pyrex8/leaf-energy-meter/images/arduino.png

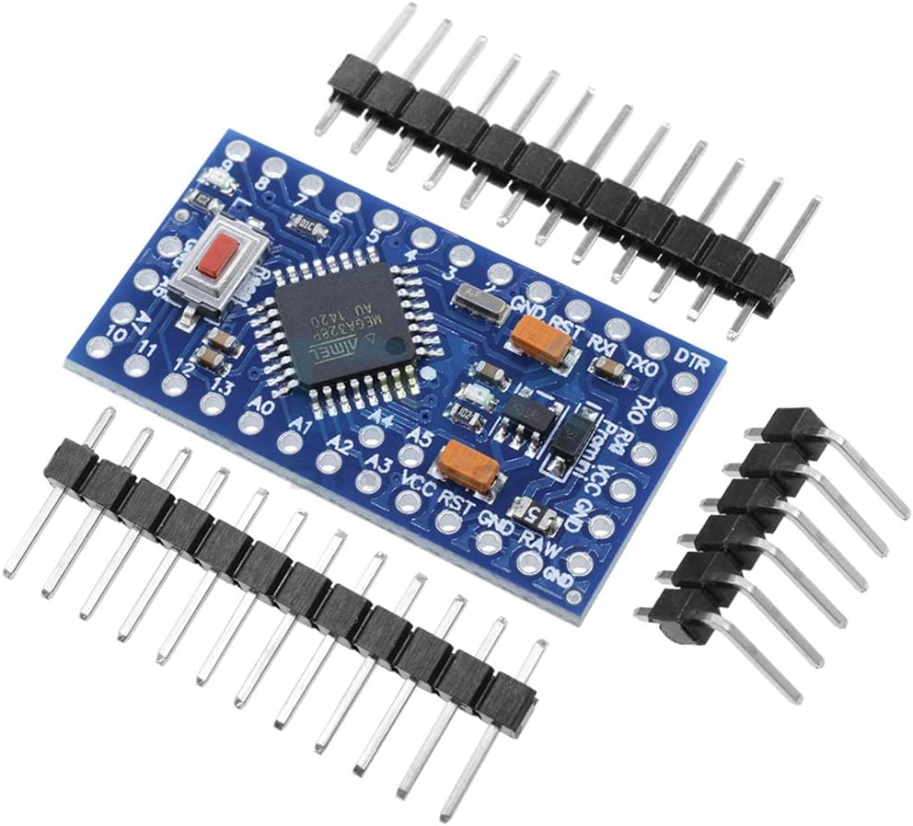
images/arduino.png
