pyrex8/leaf-energy-meter/images/can.png

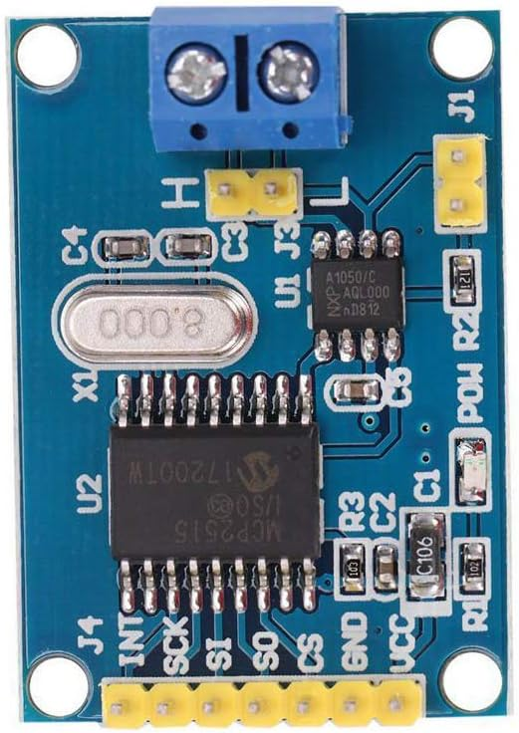
images/can.png
