pyrex8/leaf-energy-meter/images/display_bezel_black_tape.jpg

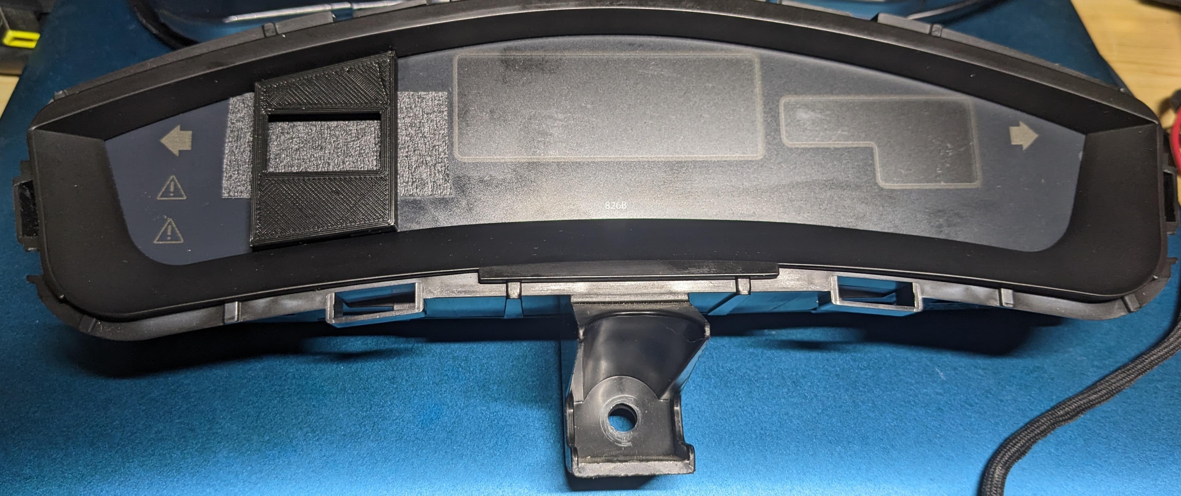
images/display_bezel_black_tape.jpg
