pyrex8/leaf-energy-meter/images/display_connector.jpg

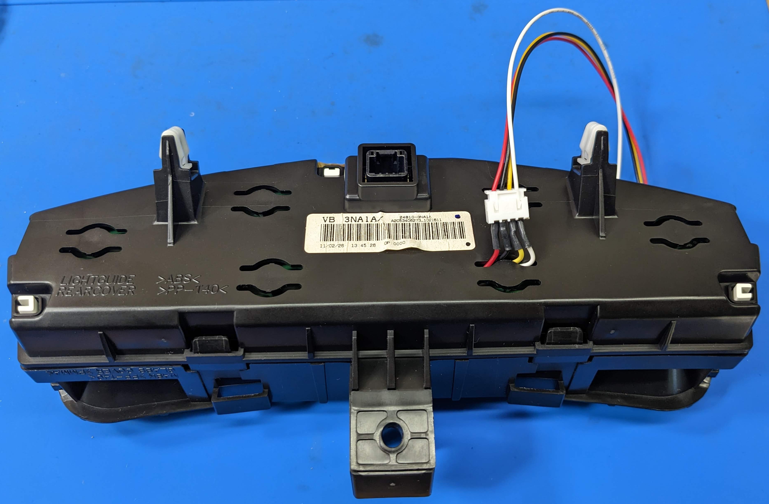
images/display_connector.jpg
