pyrex8/leaf-energy-meter/images/display_mounted.jpg

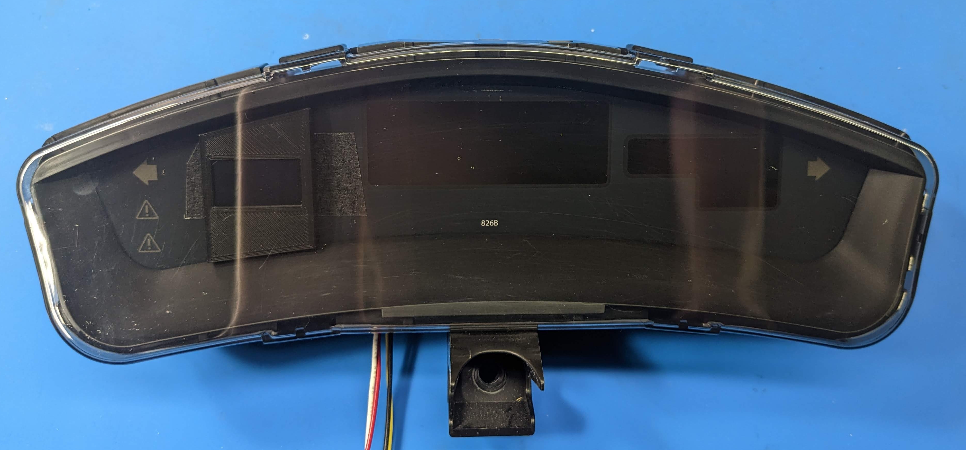
images/display_mounted.jpg
