pyrex8/leaf-energy-meter/images/enclosure.png

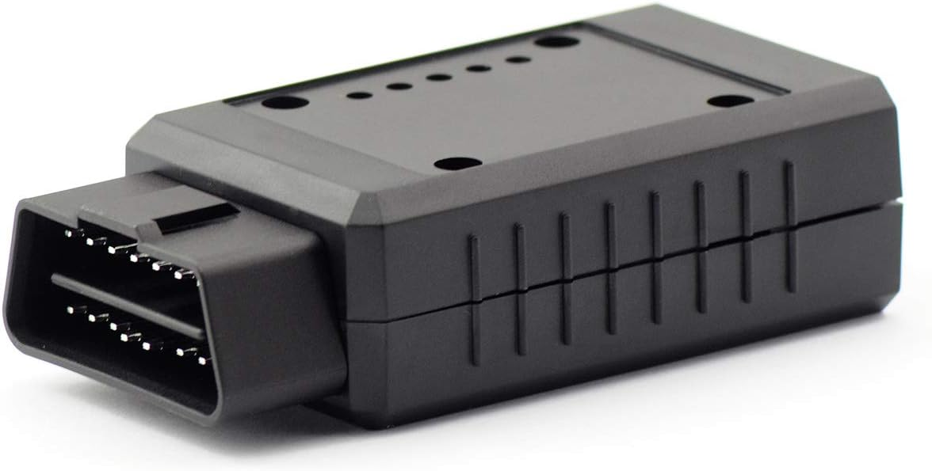
images/enclosure.png
