pyrex8/leaf-energy-meter/images/jst.png

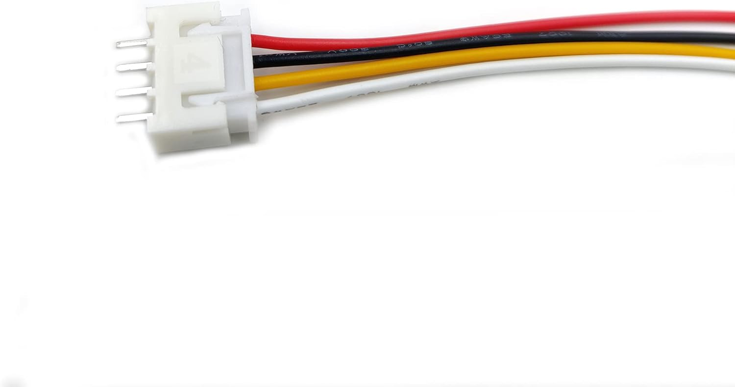
images/jst.png
