pyrex8/leaf-energy-meter/images/meter_pcb_in_case.jpg

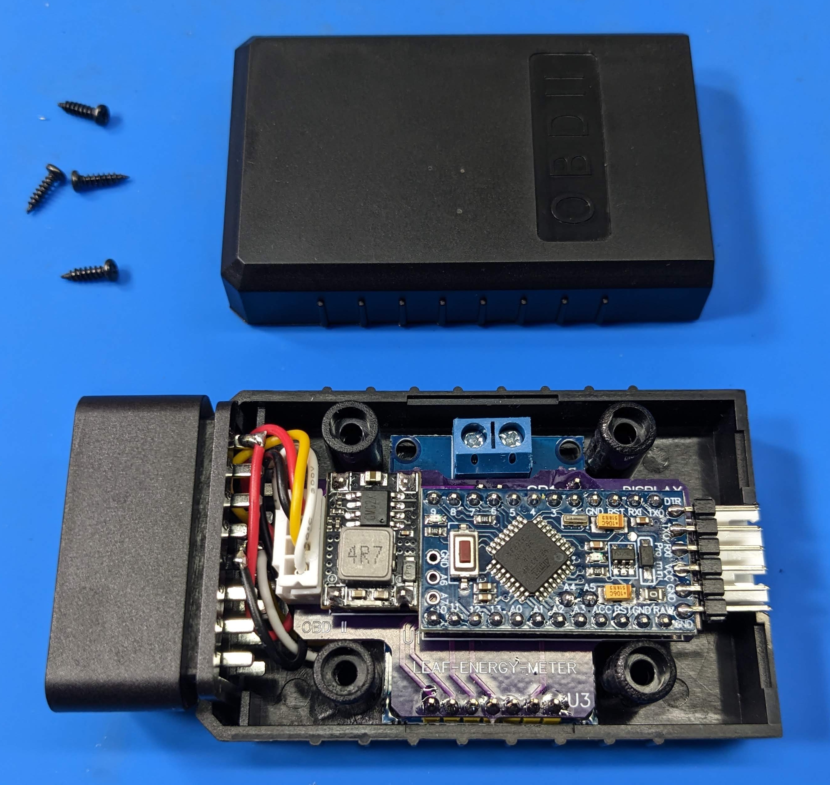
images/meter_pcb_in_case.jpg
