pyrex8/leaf-energy-meter/images/oled.png

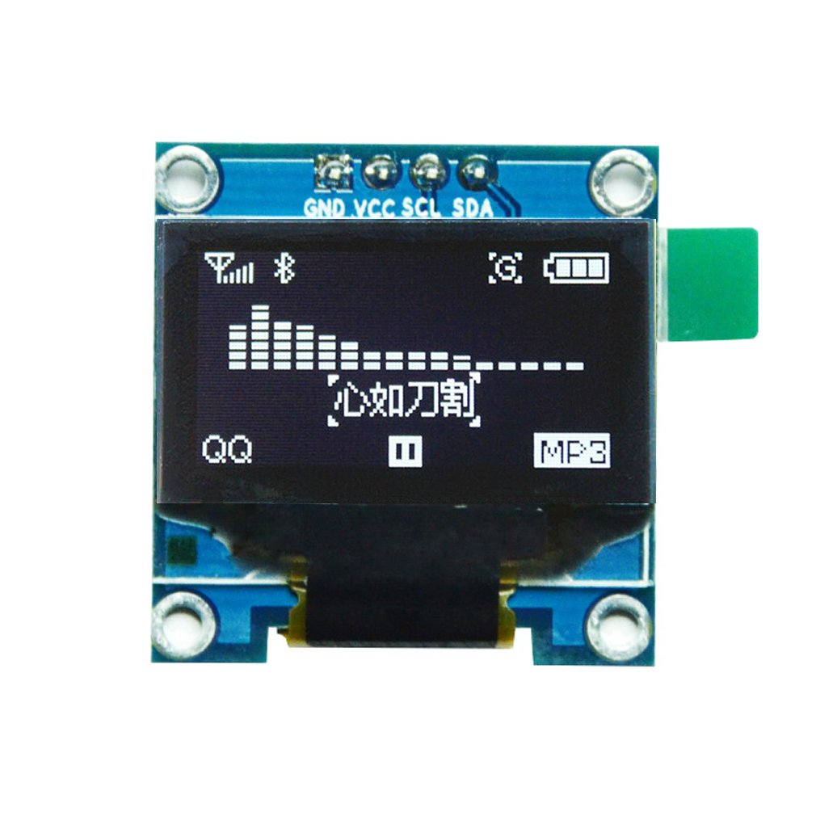
images/oled.png
