pyrex8/leaf-energy-meter/images/display_soldering.jpg

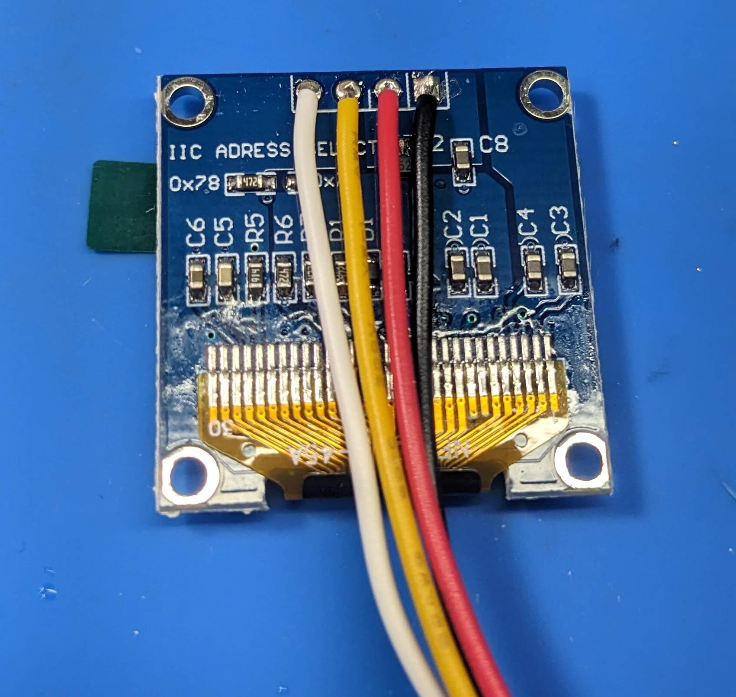
images/display_soldering.jpg
