pyrex8/leaf-energy-meter/images/obd2_male_backshell_wiring.png

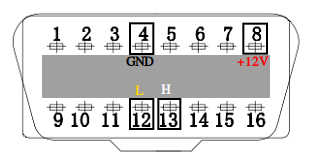
images/obd2_male_backshell_wiring.png
